pierre-bouckson/Chess-clock-using-STM32/software_STM32/app/inc/main.h

/*
 * main.h
 *
 *  Created on: 5 août 2017
 *      Author: Laurent
 */

#ifndef APP_INC_MAIN_H_
#define APP_INC_MAIN_H_


#include "stm32f0xx.h"
#include "bsp.h"

/*
 * printf() and sprintf() from printf-stdarg.c
 */


int my_printf	(const char *format, ...);
int my_sprintf	(char *out, const char *format, ...);

#endif /* APP_INC_MAIN_H_ */
