pierre-bouckson/Chess-clock-using-STM32/software_STM32/bsp/inc/rtc.h

/*
 * rtc.h
 *
 *  Created on: 20 août 2017
 *      Author: Laurent
 */

#ifndef BSP_INC_RTC_H_
#define BSP_INC_RTC_H_

#include "stm32f0xx.h"

// Typedefs
typedef struct
{
	uint8_t hours;
	uint8_t minutes;
	uint8_t seconds;
} time_t;

void BSP_RTC_Clock_Config	(void);
void BSP_RTC_EXTI_Init		(void);

void BSP_RTC_SetTime		(time_t *ptime);
void BSP_RTC_GetTime		(time_t *ptime);

void BSP_RTC_SetAlarmA		(time_t *ptime);
void BSP_RTC_GetAlarmA		(time_t *ptime);


#endif /* BSP_INC_RTC_H_ */
